GustavAbrahamsson/Gamestation-Portable/GSP_HW/include/example_code.h

void testdrawline() {
   int16_t i;

   display.clearDisplay(); // Clear display buffer

   for(i=0; i<display.width(); i+=4) {
      display.drawLine(0, 0, i, display.height()-1, SSD1306_WHITE);
      display.display(); // Update screen with each newly-drawn line
      delay(1);
   }
   for(i=0; i<display.height(); i+=4) {
      display.drawLine(0, 0, display.width()-1, i, SSD1306_WHITE);
      display.display();
      delay(1);
   }
   delay(250);

   display.clearDisplay();

   for(i=0; i<display.width(); i+=4) {
      display.drawLine(0, display.height()-1, i, 0, SSD1306_WHITE);
      display.display();
      delay(1);
   }
   for(i=display.height()-1; i>=0; i-=4) {
      display.drawLine(0, display.height()-1, display.width()-1, i, SSD1306_WHITE);
      display.display();
      delay(1);
   }
   delay(250);

   display.clearDisplay();

   for(i=display.width()-1; i>=0; i-=4) {
      display.drawLine(display.width()-1, display.height()-1, i, 0, SSD1306_WHITE);
      display.display();
      delay(1);
   }
   for(i=display.height()-1; i>=0; i-=4) {
      display.drawLine(display.width()-1, display.height()-1, 0, i, SSD1306_WHITE);
      display.display();
      delay(1);
   }
   delay(250);

   display.clearDisplay();

   for(i=0; i<display.height(); i+=4) {
      display.drawLine(display.width()-1, 0, 0, i, SSD1306_WHITE);
      display.display();
      delay(1);
   }
   for(i=0; i<display.width(); i+=4) {
      display.drawLine(display.width()-1, 0, i, display.height()-1, SSD1306_WHITE);
      display.display();
      delay(1);
   }

   delay(2000); // Pause for 2 seconds
}

void testdrawrect(void) {
   display.clearDisplay();

   for(int16_t i=0; i<display.height()/2; i+=2) {
      display.drawRect(i, i, display.width()-2*i, display.height()-2*i, SSD1306_WHITE);
      display.display(); // Update screen with each newly-drawn rectangle
      delay(1);
   }

   delay(2000);
}

void testfillrect(void) {
   display.clearDisplay();

   for(int16_t i=0; i<display.height()/2; i+=3) {
      // The INVERSE color is used so rectangles alternate white/black
      display.fillRect(i, i, display.width()-i*2, display.height()-i*2, SSD1306_INVERSE);
      display.display(); // Update screen with each newly-drawn rectangle
      delay(1);
   }

   delay(2000);
}

void testdrawcircle(void) {
   display.clearDisplay();

   for(int16_t i=0; i<max(display.width(),display.height())/2; i+=2) {
      display.drawCircle(display.width()/2, display.height()/2, i, SSD1306_WHITE);
      display.display();
      delay(1);
   }

   delay(2000);
}

void testfillcircle(void) {
   display.clearDisplay();

   for(int16_t i=max(display.width(),display.height())/2; i>0; i-=3) {
      // The INVERSE color is used so circles alternate white/black
      display.fillCircle(display.width() / 2, display.height() / 2, i, SSD1306_INVERSE);
      display.display(); // Update screen with each newly-drawn circle
      delay(1);
   }

   delay(2000);
}

void testdrawroundrect(void) {
   display.clearDisplay();

   for(int16_t i=0; i<display.height()/2-2; i+=2) {
      display.drawRoundRect(i, i, display.width()-2*i, display.height()-2*i,
         display.height()/4, SSD1306_WHITE);
      display.display();
      delay(1);
   }

   delay(2000);
}

void testfillroundrect(void) {
   display.clearDisplay();

   for(int16_t i=0; i<display.height()/2-2; i+=2) {
      // The INVERSE color is used so round-rects alternate white/black
      display.fillRoundRect(i, i, display.width()-2*i, display.height()-2*i,
         display.height()/4, SSD1306_INVERSE);
      display.display();
      delay(1);
   }

   delay(2000);
}

void testdrawtriangle(void) {
   display.clearDisplay();

   for(int16_t i=0; i<max(display.width(),display.height())/2; i+=5) {
      display.drawTriangle(
         display.width()/2  , display.height()/2-i,
         display.width()/2-i, display.height()/2+i,
         display.width()/2+i, display.height()/2+i, SSD1306_WHITE);
      display.display();
      delay(1);
   }

   delay(2000);
}

void testfilltriangle(void) {
   display.clearDisplay();

   for(int16_t i=max(display.width(),display.height())/2; i>0; i-=5) {
      // The INVERSE color is used so triangles alternate white/black
      display.fillTriangle(
         display.width()/2  , display.height()/2-i,
         display.width()/2-i, display.height()/2+i,
         display.width()/2+i, display.height()/2+i, SSD1306_INVERSE);
      display.display();
      delay(1);
   }

   delay(2000);
}

void testdrawchar(void) {
   display.clearDisplay();

   display.setTextSize(1);      // Normal 1:1 pixel scale
   display.setTextColor(SSD1306_WHITE); // Draw white text
   display.setCursor(0, 0);     // Start at top-left corner
   display.cp437(true);         // Use full 256 char 'Code Page 437' font

   // Not all the characters will fit on the display. This is normal.
   // Library will draw what it can and the rest will be clipped.
   for(int16_t i=0; i<256; i++) {
      if(i == '\n') display.write(' ');
      else          display.write(i);
   }

   display.display();
   delay(2000);
}

void testdrawstyles(void) {
   display.clearDisplay();

   display.setTextSize(1);             // Normal 1:1 pixel scale
   display.setTextColor(SSD1306_WHITE);        // Draw white text
   display.setCursor(0,0);             // Start at top-left corner
   display.println(F("Hello, world!"));

   display.setTextColor(SSD1306_BLACK, SSD1306_WHITE); // Draw 'inverse' text
   display.println(3.141592);

   display.setTextSize(2);             // Draw 2X-scale text
   display.setTextColor(SSD1306_WHITE);
   display.print(F("0x")); display.println(0xDEADBEEF, HEX);

   display.display();
   delay(2000);
}

void testscrolltext(void) {
   display.clearDisplay();

   display.setTextSize(2); // Draw 2X-scale text
   display.setTextColor(SSD1306_WHITE);
   display.setCursor(10, 0);
   display.println(F("scroll"));
   display.display();      // Show initial text
   delay(100);

   // Scroll in various directions, pausing in-between:
   display.startscrollright(0x00, 0x0F);
   delay(2000);
   display.stopscroll();
   delay(1000);
   display.startscrollleft(0x00, 0x0F);
   delay(2000);
   display.stopscroll();
   delay(1000);
   display.startscrolldiagright(0x00, 0x07);
   delay(2000);
   display.startscrolldiagleft(0x00, 0x07);
   delay(2000);
   display.stopscroll();
   delay(1000);
}

void demo(){
   // Show initial display buffer contents on the screen --
   // the library initializes this with an Adafruit splash screen.
   display.display();
   delay(2000); // Pause for 2 seconds

   // Clear the buffer
   display.clearDisplay();

   // Draw a single pixel in white
   display.drawPixel(10, 10, SSD1306_WHITE);

   // Show the display buffer on the screen. You MUST call display() after
   // drawing commands to make them visible on screen!
   display.display();
   delay(2000);
   // display.display() is NOT necessary after every single drawing command,
   // unless that's what you want...rather, you can batch up a bunch of
   // drawing operations and then update the screen all at once by calling
   // display.display(). These examples demonstrate both approaches...

   testdrawline();      // Draw many lines
   testdrawrect();      // Draw rectangles (outlines)
   testfillrect();      // Draw rectangles (filled)
   testdrawcircle();    // Draw circles (outlines)
   testfillcircle();    // Draw circles (filled)
   testdrawroundrect(); // Draw rounded rectangles (outlines)
   testfillroundrect(); // Draw rounded rectangles (filled)
   testdrawtriangle();  // Draw triangles (outlines)
   testfilltriangle();  // Draw triangles (filled)
   testdrawchar();      // Draw characters of the default font
   testdrawstyles();    // Draw 'stylized' characters
   testscrolltext();    // Draw scrolling text
   
   // Invert and restore display, pausing in-between
   display.invertDisplay(true);
   delay(1000);
   display.invertDisplay(false);
   delay(1000);
}
